gpeter62/ESP_UniClock/Datasheets/iv-9-datasheet.gif

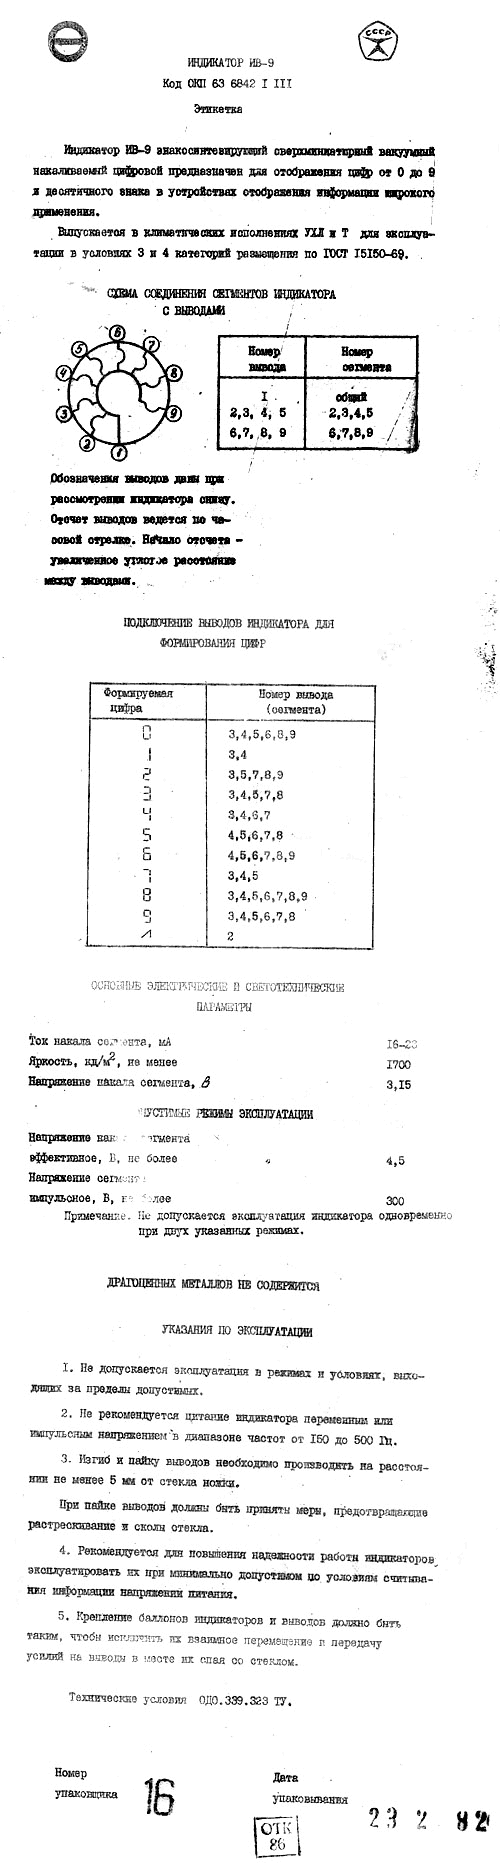
Datasheets/iv-9-datasheet.gif
