gpeter62/ESP_UniClock/Datasheets/iv-16-datasheet.jpg

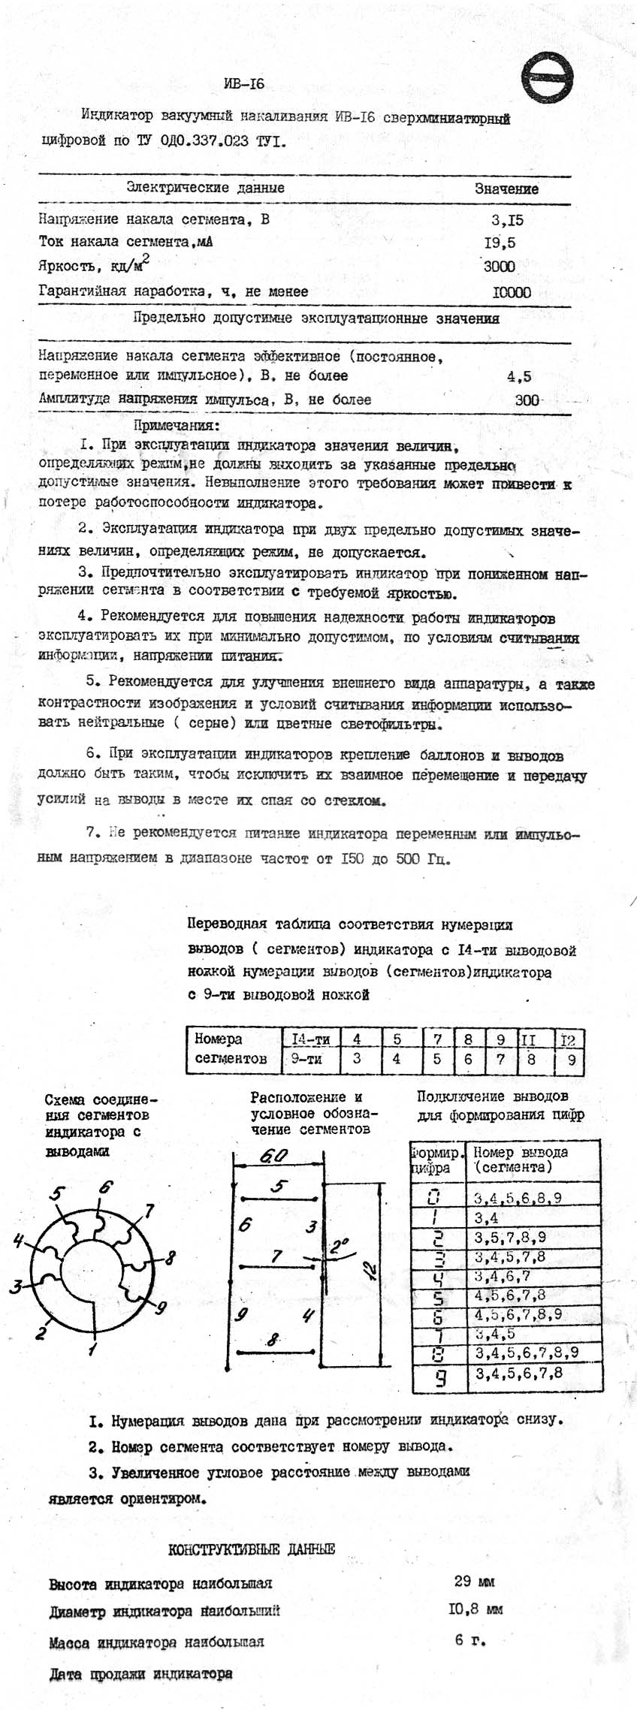
Datasheets/iv-16-datasheet.jpg
