gpeter62/ESP_UniClock/neopixel_adafruit.ino

#ifdef USE_NEOPIXEL_ADAFRUIT

#include <Adafruit_NeoPixel.h>

#define PixelPin 3
int PixelCount = maxDigits;

// Parameter 1 = number of pixels in strip
// Parameter 2 = Arduino pin number (most are valid)
// Parameter 3 = pixel type flags, add together as needed:
//   NEO_KHZ800  800 KHz bitstream (most NeoPixel products w/WS2812 LEDs)
//   NEO_KHZ400  400 KHz (classic 'v1' (not v2) FLORA pixels, WS2811 drivers)
//   NEO_GRB     Pixels are wired for GRB bitstream (most NeoPixel products)
//   NEO_RGB     Pixels are wired for RGB bitstream (v1 FLORA pixels, not v2)
//   NEO_RGBW    Pixels are wired for RGBW bitstream (NeoPixel RGBW products)
Adafruit_NeoPixel strip = Adafruit_NeoPixel(PixelCount, PixelPin, NEO_GRB + NEO_KHZ800);

#define COLORSATURATION 255
#define DO_ANIMATION true   //true or false
#define LED_ANIM_SPEED 100

uint8_t c_MinBrightness = 8; 
uint8_t c_MaxBrightness = 80;
byte neoBrightness;
  
void setupNeopixelAdafruit() {  
  DPRINTLN("Setup NeoPixel LEDS (Adafruit lib):");
  DPRINT("Pixel count: "); DPRINTLN(PixelCount);
  DPRINT("Brightness:"); DPRINT(c_MinBrightness); DPRINT(" - "); DPRINTLN(c_MaxBrightness);
  neoBrightness = prm.dayBright * ((c_MaxBrightness - c_MinBrightness)/MAXBRIGHTNESS);  
  strip.begin();
  strip.setBrightness(neoBrightness);
  strip.show(); // Initialize all pixels to 'off'
  rainbow(1);
}

void doAnimationAdafruit() {
  
  neoBrightness = (displayON ?  prm.dayBright : 0) * ((c_MaxBrightness - c_MinBrightness)/MAXBRIGHTNESS);
  strip.setBrightness(neoBrightness);
    
  // Some example procedures showing how to display to the pixels:
  //colorWipe(strip.Color(255, 0, 0), 50); // Red
  //colorWipe(strip.Color(0, 255, 0), 50); // Green
  //colorWipe(strip.Color(0, 0, 255), 50); // Blue
  //colorWipe(strip.Color(0, 0, 0, 255), 50); // White RGBW
  // Send a theater pixel chase in...
  //theaterChase(strip.Color(127, 127, 127), 50); // White
  //theaterChase(strip.Color(127, 0, 0), 50); // Red
  //theaterChase(strip.Color(0, 0, 127), 50); // Blue
  //theaterChaseRainbow(50);
  
  if (DO_ANIMATION) {
    rainbow(LED_ANIM_SPEED);
    //rainbowCycle(LED_ANIM_SPEED);
  }
}

  // Fill the dots one after the other with a color
void colorWipe(uint32_t c, uint8_t wait) {
  for(uint16_t i=0; i<strip.numPixels(); i++) {
    strip.setPixelColor(i, c);
    strip.show();
    delay(wait);
  }
}

void rainbow(uint8_t wait) {
static uint16_t j;
static unsigned long lastRun = 0;
uint16_t i; 

  if ((millis()-lastRun)<wait) return;
  lastRun = millis();

  for(i=0; i<strip.numPixels(); i++) {
      strip.setPixelColor(i, Wheel((i+j) & 255));
  }
  strip.show();
  j++; if (j>255) j=0;
}

// Slightly different, this makes the rainbow equally distributed throughout
void rainbowCycle(uint8_t wait) {
static uint16_t j;
static unsigned long lastRun = 0;
uint16_t i;

  if ((millis()-lastRun)<wait) return;
  lastRun = millis();
  for(i=0; i< strip.numPixels(); i++) {
    strip.setPixelColor(i, Wheel(((i * 256 / strip.numPixels()) + j) & 255));
  }
  strip.show();
  j++; if (j>255) j=0;
}

//Theatre-style crawling lights.
void theaterChase(uint32_t c, uint8_t wait) {
  for (int j=0; j<10; j++) {  //do 10 cycles of chasing
    for (int q=0; q < 3; q++) {
      for (uint16_t i=0; i < strip.numPixels(); i=i+3) {
        strip.setPixelColor(i+q, c);    //turn every third pixel on
      }
      strip.show();

      delay(wait);

      for (uint16_t i=0; i < strip.numPixels(); i=i+3) {
        strip.setPixelColor(i+q, 0);        //turn every third pixel off
      }
    }
  }
}

//Theatre-style crawling lights with rainbow effect
void theaterChaseRainbow(uint8_t wait) {
  for (int j=0; j < 256; j++) {     // cycle all 256 colors in the wheel
    for (int q=0; q < 3; q++) {
      for (uint16_t i=0; i < strip.numPixels(); i=i+3) {
        strip.setPixelColor(i+q, Wheel( (i+j) % 255));    //turn every third pixel on
      }
      strip.show();

      delay(wait);

      for (uint16_t i=0; i < strip.numPixels(); i=i+3) {
        strip.setPixelColor(i+q, 0);        //turn every third pixel off
      }
    }
  }
}

// Input a value 0 to 255 to get a color value.
// The colours are a transition r - g - b - back to r.
uint32_t Wheel(byte WheelPos) {
  WheelPos = 255 - WheelPos;
  if(WheelPos < 85) {
    return strip.Color(255 - WheelPos * 3, 0, WheelPos * 3);
  }
  if(WheelPos < 170) {
    WheelPos -= 85;
    return strip.Color(0, WheelPos * 3, 255 - WheelPos * 3);
  }
  WheelPos -= 170;
  return strip.Color(WheelPos * 3, 255 - WheelPos * 3, 0);
}
#else
void setupNeopixelAdafruit() {}
void doAnimationAdafruit() {}
#endif
