gpeter62/ESP_UniClock/DHT_temp.ino

#ifdef USE_DHT_TEMP
// REQUIRES the following Arduino libraries:
// - DHT Sensor Library: https://github.com/adafruit/DHT-sensor-library
// - Adafruit Unified Sensor Lib: https://github.com/adafruit/Adafruit_Sensor

#include "DHT.h"
// TEMP_SENSOR_PIN is used to connect the sensor
// Feather HUZZAH ESP8266 note: use pins 3, 4, 5, 12, 13 or 14 --
// Pin 15 can work but DHT must be disconnected during program upload.

// Uncomment whatever type you're using!
#define DHTTYPE DHT11   // DHT 11
//#define DHTTYPE DHT22   // DHT 22  (AM2302), AM2321
//#define DHTTYPE DHT21   // DHT 21 (AM2301)

// Connect pin 1 (on the left) of the sensor to +5V
// NOTE: If using a board with 3.3V logic like an Arduino Due connect pin 1
// to 3.3V instead of 5V!
// Connect pin 2 of the sensor to whatever your DHTPIN is
// Connect pin 4 (on the right) of the sensor to GROUND
// Connect a 10K resistor from pin 2 (data) to pin 1 (power) of the sensor

// Initialize DHT sensor.
// Note that older versions of this library took an optional third parameter to
// tweak the timings for faster processors.  This parameter is no longer needed
// as the current DHT reading algorithm adjusts itself to work on faster procs.
DHT dht(TEMP_SENSOR_PIN, DHTTYPE);

void setupDHTemp() {
  DPRINT("DHTxx setup: Sensor pin = "); DPRINTLN(TEMP_SENSOR_PIN);
  dht.begin();
  getDHTemp();
}

void getDHTemp() {
static unsigned long lastRun = 0;

  if (((millis()-lastRun)<2500) || (second()!=0)) return;
  lastRun = millis();  

  // Reading temperature or humidity takes about 250 milliseconds!
  // Sensor readings may also be up to 2 seconds 'old' (its a very slow sensor)
  humid = dht.readHumidity();
  temperature[0] = dht.readTemperature();      // Read temperature as Celsius (the default)
  useTemp = 1;
  useHumid = 1;
  //DPRINT(temperature[0]); DPRINT("C  "); DPRINT(humid); DPRINTLN("%");
  // Read temperature as Fahrenheit (isFahrenheit = true)
  //float f = dht.readTemperature(true);   Compute heat index in Fahrenheit (the default)
  //float hif = dht.computeHeatIndex(f, h);
  
  //float hic = dht.computeHeatIndex(t, h, false);  // Compute heat index in Celsius (isFahreheit = false)
  
  if (isnan(humid) || isnan(temperature[0])) {  // Check if any reads failed and exit early (to try again).
    DPRINTLN("No sensor!");
    useTemp = 1;
    temperature[0] = 99.9f;
    humid = 0;
    useHumid = 0;
  }
}

#else
void setupDHTemp() {}
void getDHTemp() {}
#endif
